bobby1321/Colossus-Of-Codes/SCD/MK1/keyboard_mk1.kicad_sch

## KiCad design SCD/MK1/keyboard_mk1.kicad_sch (2023-07-09)

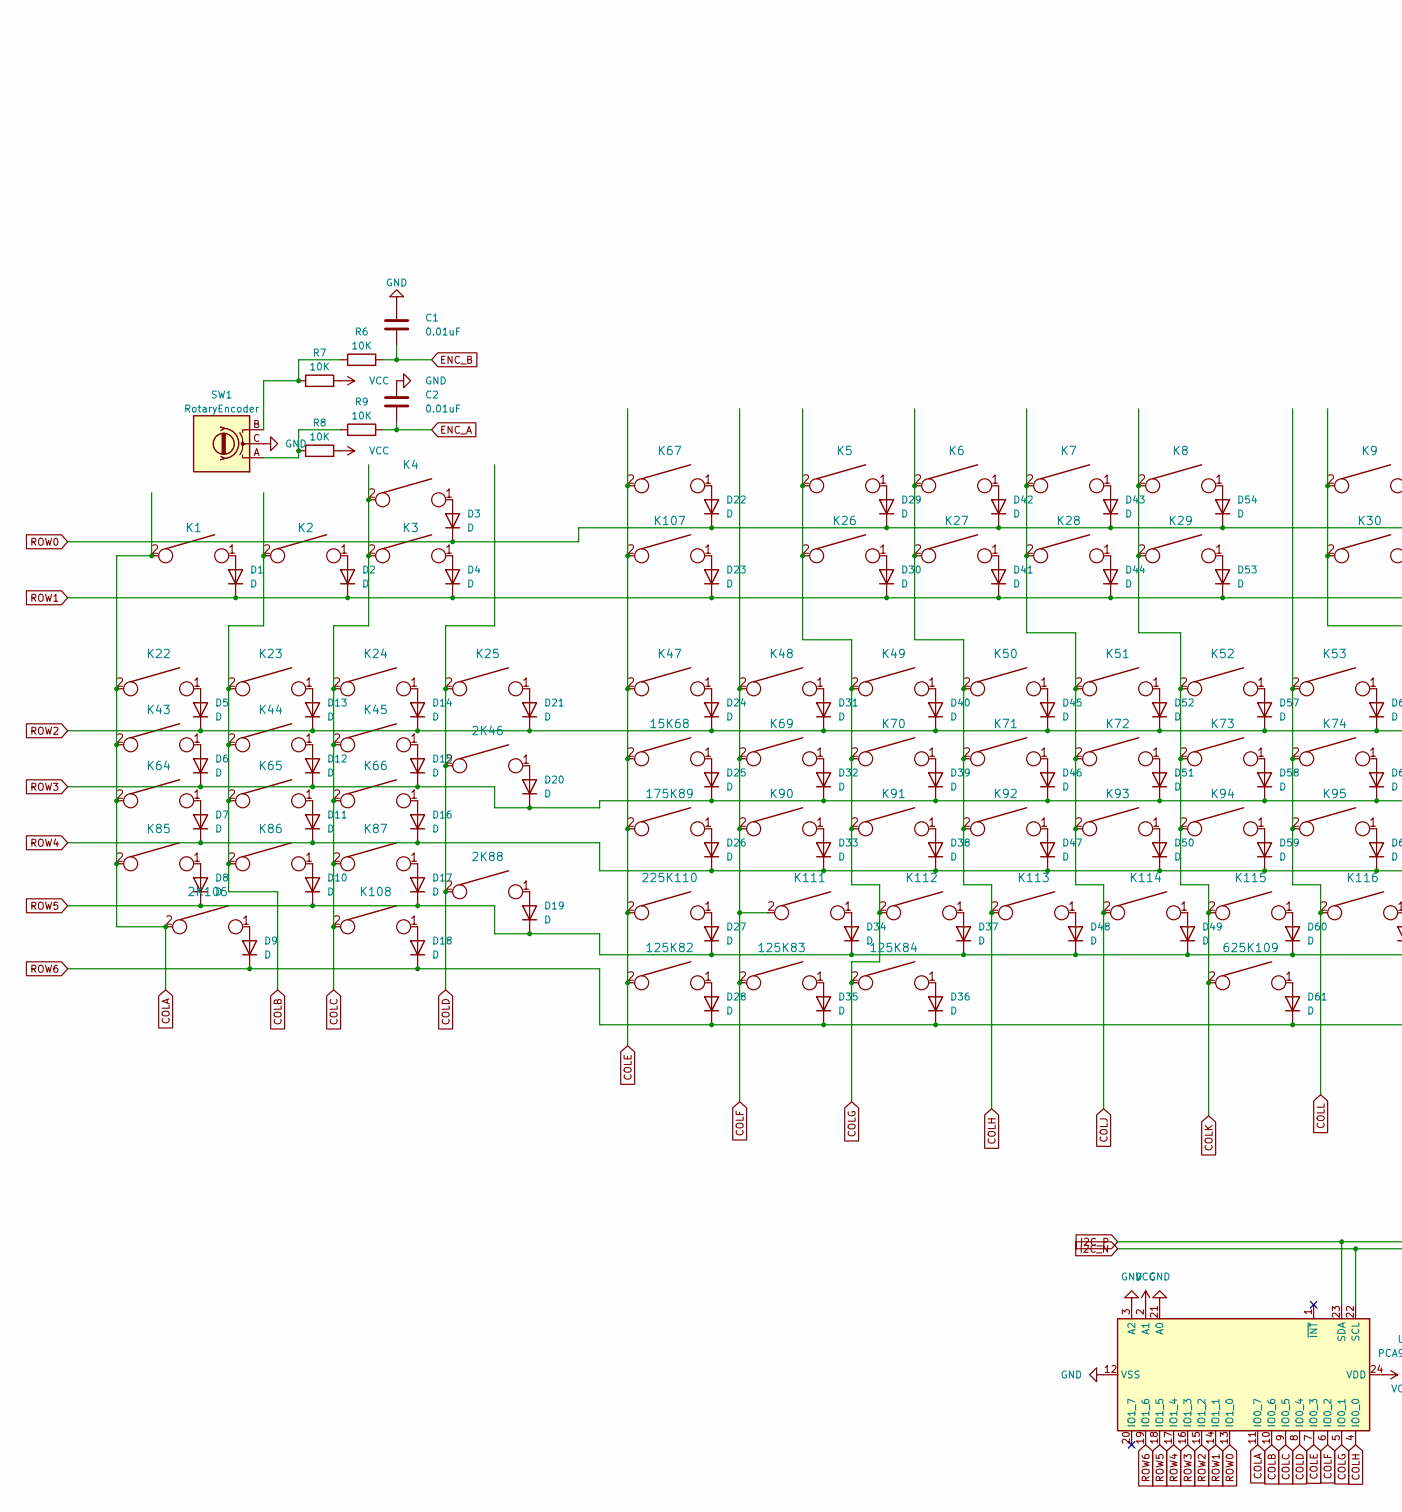
[picture p12: schematic keyboard_mk1.kicad_sch, part in row 1, column 1]

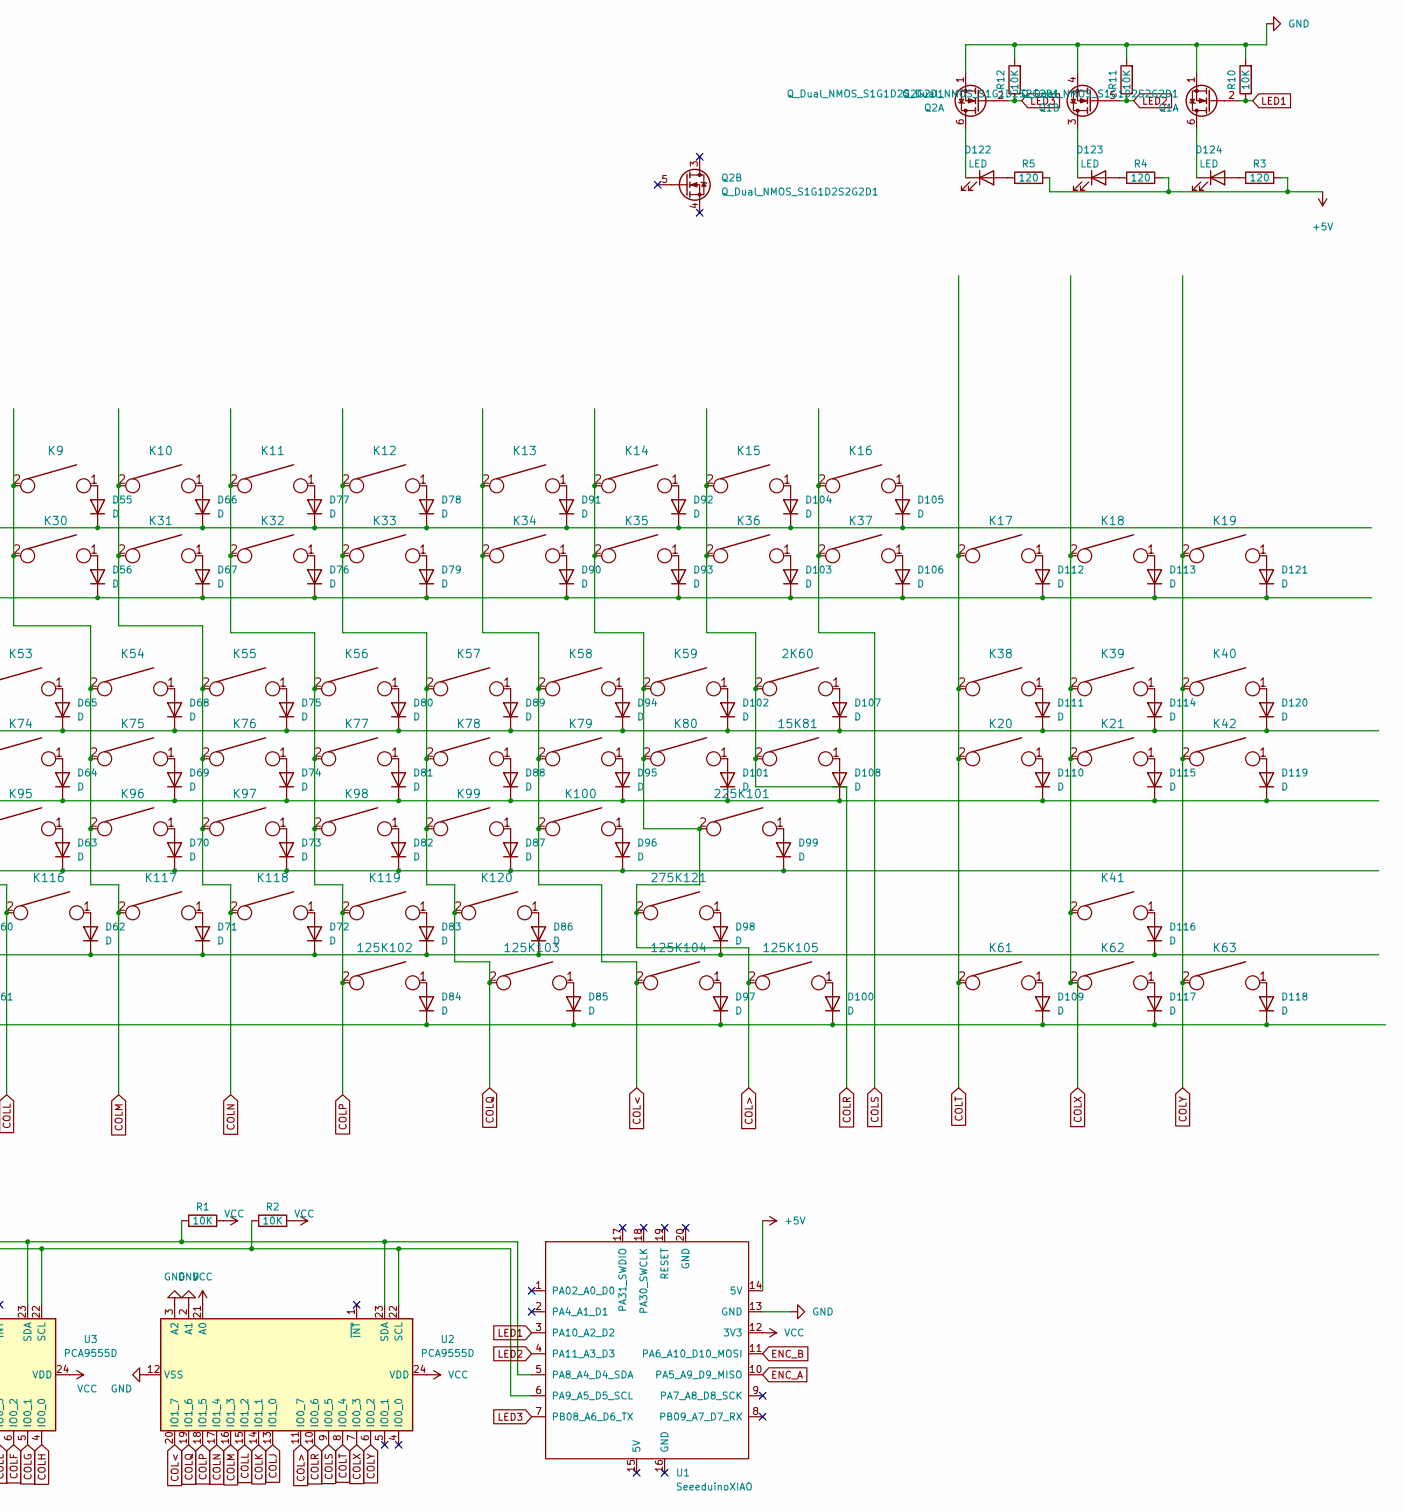
[picture p13: schematic keyboard_mk1.kicad_sch, part in row 1, column 2]

Parts:
2K46, 2K60, 2K88, 2K106: KEYSW; MXOnly-2U-Hotswap
15K68, 15K81: KEYSW; MXOnly-1.5U-Hotswap
125K82, 125K83, 125K84, 125K102, 125K103, 125K104, 125K105: KEYSW; MXOnly-1.25U-Hotswap
175K89: KEYSW; MXOnly-1.75U-Hotswap
225K101, 225K110: KEYSW; MXOnly-2.25U-Hotswap
275K121: KEYSW; MXOnly-2.75U-Hotswap
625K109: KEYSW; MXOnly-6.25U-Hotswap
C1, C2: 0.01uF; C_0805_2012Metric_Pad1.18x1.45mm_HandSolder
D1, D2, D3, D4, D5, D6, D7, D8, D9, D10, D11, D12, D13, D14, D15, D16, D17, D18, D19, D20, D21, D22, D23, D24, D25, D26, D27, D28, D29, D30, D31, D32, D33, D34, D35, D36, D37, D38, D39, D40, D41, D42, D43, D44, D45, D46, D47, D48, D49, D50, D51, D52, D53, D54, D55, D56, D57, D58, D59, D60, D61, D62, D63, D64, D65, D66, D67, D68, D69, D70, D71, D72, D73, D74, D75, D76, D77, D78, D79, D80, D81, D82, D83, D84, D85, D86, D87, D88, D89, D90, D91, D92, D93, D94, D95, D96, D97, D98, D99, D100, D101, D102, D103, D104, D105, D106, D107, D108, D109, D110, D111, D112, D113, D114, D115, D116, D117, D118, D119, D120, D121: D; D_SOD-123
D122, D123, D124: LED; LED_0805_2012Metric_Pad1.15x1.40mm_HandSolder
K1, K2, K3, K4, K5, K6, K7, K8, K9, K10, K11, K12, K13, K14, K15, K16, K17, K18, K19, K20, K21, K22, K23, K24, K25, K26, K27, K28, K29, K30, K31, K32, K33, K34, K35, K36, K37, K38, K39, K40, K41, K42, K43, K44, K45, K47, K48, K49, K50, K51, K52, K53, K54, K55, K56, K57, K58, K59, K61, K62, K63, K64, K65, K66, K67, K69, K70, K71, K72, K73, K74, K75, K76, K77, K78, K79, K80, K85, K86, K87, K90, K91, K92, K93, K94, K95, K96, K97, K98, K99, K100, K107, K108, K111, K112, K113, K114, K115, K116, K117, K118, K119, K120: KEYSW; MXOnly-1U-Hotswap
Q1, Q2: Q_Dual_NMOS_S1G1D2S2G2D1; SOT-363_SC-70-6_Handsoldering
R1, R2, R6, R7, R8, R9, R10, R11, R12: 10K; R_0805_2012Metric_Pad1.20x1.40mm_HandSolder
R3, R4, R5: 120; R_0805_2012Metric_Pad1.20x1.40mm_HandSolder
SW1: RotaryEncoder; PinHeader_1x03_P2.54mm_Horizontal
U1: SeeeduinoXIAO; Seeeduino XIAO-MOUDLE14P-2.54-21X17.8MM
U2, U3: PCA9555D; SOIC-24W_7.5x15.4mm_P1.27mm

Connections:
+5V: R3.2, R4.2, R5.2, U1.14 (5V)
COL<: 125K104.2, K13.2, K34.2, K58.2, K79.2, K100.2, U2.20 (IO1_7)
COL>: 125K105.2, 225K101.2, 275K121.2, K14.2, K35.2, K59.2, K80.2, U2.11 (IO0_7)
COLA: 2K106.2, K1.2, K22.2, K43.2, K64.2, K85.2, U3.11 (IO0_7)
COLB: K2.2, K23.2, K44.2, K65.2, K86.2, U3.10 (IO0_6)
COLC: K3.2, K4.2, K24.2, K45.2, K66.2, K87.2, K108.2, U3.9 (IO0_5)
COLD: 2K46.2, 2K88.2, K25.2, U3.8 (IO0_4)
COLE: 15K68.2, 125K82.2, 175K89.2, 225K110.2, K47.2, K67.2, K107.2, U3.7 (IO0_3)
COLF: 125K83.2, K48.2, K69.2, K90.2, K111.2, U3.6 (IO0_2)
COLG: 125K84.2, K5.2, K26.2, K49.2, K70.2, K91.2, K112.2, U3.5 (IO0_1)
COLH: K6.2, K27.2, K50.2, K71.2, K92.2, K113.2, U3.4 (IO0_0)
COLJ: K7.2, K28.2, K51.2, K72.2, K93.2, K114.2, U2.13 (IO1_0)
COLK: 625K109.2, K8.2, K29.2, K52.2, K73.2, K94.2, K115.2, U2.14 (IO1_1)
COLL: K53.2, K74.2, K95.2, K116.2, U2.15 (IO1_2)
COLM: K9.2, K30.2, K54.2, K75.2, K96.2, K117.2, U2.16 (IO1_3)
COLN: K10.2, K31.2, K55.2, K76.2, K97.2, K118.2, U2.17 (IO1_4)
COLP: 125K102.2, K11.2, K32.2, K56.2, K77.2, K98.2, K119.2, U2.18 (IO1_5)
COLQ: 125K103.2, K12.2, K33.2, K57.2, K78.2, K99.2, K120.2, U2.19 (IO1_6)
COLR: 2K60.2, 15K81.2, K15.2, K36.2, U2.10 (IO0_6)
COLS: K16.2, K37.2, U2.9 (IO0_5)
COLT: K17.2, K20.2, K38.2, K61.2, U2.8 (IO0_4)
COLX: K18.2, K21.2, K39.2, K41.2, K62.2, U2.7 (IO0_3)
COLY: K19.2, K40.2, K42.2, K63.2, U2.6 (IO0_2)
ENC_A: C2.2, R9.2, U1.10 (PA5_A9_D9_MISO)
ENC_B: C1.2, R6.2, U1.11 (PA6_A10_D10_MOSI)
GND: C1.1, C2.1, Q1.1 (S), Q1.4 (S), Q2.1 (S), R10.2, R11.2, R12.2, SW1.C, U1.13 (GND), U2.2 (A1), U2.3 (A2), U2.12 (VSS), U3.3 (A2), U3.12 (VSS), U3.21 (A0)
I2C_N: R2.1, U1.6 (PA9_A5_D5_SCL), U2.22 (SCL), U3.22 (SCL)
I2C_P: R1.1, U1.5 (PA8_A4_D4_SDA), U2.23 (SDA), U3.23 (SDA)
LED1: Q1.2 (G), R10.1, U1.3 (PA10_A2_D2)
LED2: Q1.5 (G), R11.1, U1.4 (PA11_A3_D3)
LED3: Q2.2 (G), R12.1, U1.7 (PB08_A6_D6_TX)
unnamed: 2K46.1, D20.2 (A)
unnamed: 2K60.1, D107.2 (A)
unnamed: 2K88.1, D19.2 (A)
unnamed: 2K106.1, D9.2 (A)
unnamed: 15K68.1, D25.2 (A)
unnamed: 15K81.1, D108.2 (A)
unnamed: 125K82.1, D28.2 (A)
unnamed: 125K83.1, D35.2 (A)
unnamed: 125K84.1, D36.2 (A)
unnamed: 125K102.1, D84.2 (A)
unnamed: 125K103.1, D85.2 (A)
unnamed: 125K104.1, D97.2 (A)
unnamed: 125K105.1, D100.2 (A)
unnamed: 175K89.1, D26.2 (A)
unnamed: 225K101.1, D99.2 (A)
unnamed: 225K110.1, D27.2 (A)
unnamed: 275K121.1, D98.2 (A)
unnamed: 625K109.1, D61.2 (A)
unnamed: D1.2 (A), K1.1
unnamed: D2.2 (A), K2.1
unnamed: D3.2 (A), K4.1
unnamed: D4.2 (A), K3.1
unnamed: D5.2 (A), K22.1
unnamed: D6.2 (A), K43.1
unnamed: D7.2 (A), K64.1
unnamed: D8.2 (A), K85.1
unnamed: D10.2 (A), K86.1
unnamed: D11.2 (A), K65.1
unnamed: D12.2 (A), K44.1
unnamed: D13.2 (A), K23.1
unnamed: D14.2 (A), K24.1
unnamed: D15.2 (A), K45.1
unnamed: D16.2 (A), K66.1
unnamed: D17.2 (A), K87.1
unnamed: D18.2 (A), K108.1
unnamed: D21.2 (A), K25.1
unnamed: D22.2 (A), K67.1
unnamed: D23.2 (A), K107.1
unnamed: D24.2 (A), K47.1
unnamed: D29.2 (A), K5.1
unnamed: D30.2 (A), K26.1
unnamed: D31.2 (A), K48.1
unnamed: D32.2 (A), K69.1
unnamed: D33.2 (A), K90.1
unnamed: D34.2 (A), K111.1
unnamed: D37.2 (A), K112.1
unnamed: D38.2 (A), K91.1
unnamed: D39.2 (A), K70.1
unnamed: D40.2 (A), K49.1
unnamed: D41.2 (A), K27.1
unnamed: D42.2 (A), K6.1
unnamed: D43.2 (A), K7.1
unnamed: D44.2 (A), K28.1
unnamed: D45.2 (A), K50.1
unnamed: D46.2 (A), K71.1
unnamed: D47.2 (A), K92.1
unnamed: D48.2 (A), K113.1
unnamed: D49.2 (A), K114.1
unnamed: D50.2 (A), K93.1
unnamed: D51.2 (A), K72.1
unnamed: D52.2 (A), K51.1
unnamed: D53.2 (A), K29.1
unnamed: D54.2 (A), K8.1
unnamed: D55.2 (A), K9.1
unnamed: D56.2 (A), K30.1
unnamed: D57.2 (A), K52.1
unnamed: D58.2 (A), K73.1
unnamed: D59.2 (A), K94.1
unnamed: D60.2 (A), K115.1
unnamed: D62.2 (A), K116.1
unnamed: D63.2 (A), K95.1
unnamed: D64.2 (A), K74.1
unnamed: D65.2 (A), K53.1
unnamed: D66.2 (A), K10.1
unnamed: D67.2 (A), K31.1
unnamed: D68.2 (A), K54.1
unnamed: D69.2 (A), K75.1
unnamed: D70.2 (A), K96.1
unnamed: D71.2 (A), K117.1
unnamed: D72.2 (A), K118.1
unnamed: D73.2 (A), K97.1
unnamed: D74.2 (A), K76.1
unnamed: D75.2 (A), K55.1
unnamed: D76.2 (A), K32.1
unnamed: D77.2 (A), K11.1
unnamed: D78.2 (A), K12.1
unnamed: D79.2 (A), K33.1
unnamed: D80.2 (A), K56.1
unnamed: D81.2 (A), K77.1
unnamed: D82.2 (A), K98.1
unnamed: D83.2 (A), K119.1
unnamed: D86.2 (A), K120.1
unnamed: D87.2 (A), K99.1
unnamed: D88.2 (A), K78.1
unnamed: D89.2 (A), K57.1
unnamed: D90.2 (A), K34.1
unnamed: D91.2 (A), K13.1
unnamed: D92.2 (A), K14.1
unnamed: D93.2 (A), K35.1
unnamed: D94.2 (A), K58.1
unnamed: D95.2 (A), K79.1
unnamed: D96.2 (A), K100.1
unnamed: D101.2 (A), K80.1
unnamed: D102.2 (A), K59.1
unnamed: D103.2 (A), K36.1
unnamed: D104.2 (A), K15.1
unnamed: D105.2 (A), K16.1
unnamed: D106.2 (A), K37.1
unnamed: D109.2 (A), K61.1
unnamed: D110.2 (A), K20.1
unnamed: D111.2 (A), K38.1
unnamed: D112.2 (A), K17.1
unnamed: D113.2 (A), K18.1
unnamed: D114.2 (A), K39.1
unnamed: D115.2 (A), K21.1
unnamed: D116.2 (A), K41.1
unnamed: D117.2 (A), K62.1
unnamed: D118.2 (A), K63.1
unnamed: D119.2 (A), K42.1
unnamed: D120.2 (A), K40.1
unnamed: D121.2 (A), K19.1
unnamed: D122.1 (K), Q2.6 (D)
unnamed: D122.2 (A), R5.1
unnamed: D123.1 (K), Q1.3 (D)
unnamed: D123.2 (A), R4.1
unnamed: D124.1 (K), Q1.6 (D)
unnamed: D124.2 (A), R3.1
unnamed: R6.1, R7.1, SW1.B
unnamed: R8.1, R9.1, SW1.A
ROW0: D3.1 (K), D22.1 (K), D29.1 (K), D42.1 (K), D43.1 (K), D54.1 (K), D55.1 (K), D66.1 (K), D77.1 (K), D78.1 (K), D91.1 (K), D92.1 (K), D104.1 (K), D105.1 (K), U3.13 (IO1_0)
ROW1: D1.1 (K), D2.1 (K), D4.1 (K), D23.1 (K), D30.1 (K), D41.1 (K), D44.1 (K), D53.1 (K), D56.1 (K), D67.1 (K), D76.1 (K), D79.1 (K), D90.1 (K), D93.1 (K), D103.1 (K), D106.1 (K), D112.1 (K), D113.1 (K), D121.1 (K), U3.14 (IO1_1)
ROW2: D5.1 (K), D13.1 (K), D14.1 (K), D21.1 (K), D24.1 (K), D31.1 (K), D40.1 (K), D45.1 (K), D52.1 (K), D57.1 (K), D65.1 (K), D68.1 (K), D75.1 (K), D80.1 (K), D89.1 (K), D94.1 (K), D102.1 (K), D107.1 (K), D111.1 (K), D114.1 (K), D120.1 (K), U3.15 (IO1_2)
ROW3: D6.1 (K), D12.1 (K), D15.1 (K), D20.1 (K), D25.1 (K), D32.1 (K), D39.1 (K), D46.1 (K), D51.1 (K), D58.1 (K), D64.1 (K), D69.1 (K), D74.1 (K), D81.1 (K), D88.1 (K), D95.1 (K), D101.1 (K), D108.1 (K), D110.1 (K), D115.1 (K), D119.1 (K), U3.16 (IO1_3)
ROW4: D7.1 (K), D11.1 (K), D16.1 (K), D26.1 (K), D33.1 (K), D38.1 (K), D47.1 (K), D50.1 (K), D59.1 (K), D63.1 (K), D70.1 (K), D73.1 (K), D82.1 (K), D87.1 (K), D96.1 (K), D99.1 (K), U3.17 (IO1_4)
ROW5: D8.1 (K), D10.1 (K), D17.1 (K), D19.1 (K), D27.1 (K), D34.1 (K), D37.1 (K), D48.1 (K), D49.1 (K), D60.1 (K), D62.1 (K), D71.1 (K), D72.1 (K), D83.1 (K), D86.1 (K), D98.1 (K), D116.1 (K), U3.18 (IO1_5)
ROW6: D9.1 (K), D18.1 (K), D28.1 (K), D35.1 (K), D36.1 (K), D61.1 (K), D84.1 (K), D85.1 (K), D97.1 (K), D100.1 (K), D109.1 (K), D117.1 (K), D118.1 (K), U3.19 (IO1_6)
VCC: R1.2, R2.2, R7.2, R8.2, U1.12 (3V3), U2.21 (A0), U2.24 (VDD), U3.2 (A1), U3.24 (VDD)
